Tuna-Luna/Team5_Alligaeator/src/project/nutrition_db.py

# nutrition_db.py 
FOOD_DB = {
    0: {"food": "bean sprouts",     "kcal": 155, "protein": 13.0, "carbs": 1.1, "fat": 11.0},
    1: {"food": "beef", "kcal": 239, "protein": 27.0, "carbs": 0.0, "fat": 14.0},
    2: {"food": "chicken",  "kcal": 149, "protein": 6.4,  "carbs": 33.0, "fat": 0.5},
    3: {"food": "egg",     "kcal": 155, "protein": 13.0, "carbs": 1.1, "fat": 11.0},
    4: {"food": "fork", "kcal": 239, "protein": 27.0, "carbs": 0.0, "fat": 14.0},
    5: {"food": "garlic",  "kcal": 149, "protein": 6.4,  "carbs": 33.0, "fat": 0.5},
    6: {"food": "green onion",     "kcal": 155, "protein": 13.0, "carbs": 1.1, "fat": 11.0},
    7: {"food": "kimchi", "kcal": 239, "protein": 27.0, "carbs": 0.0, "fat": 14.0},
    8: {"food": "onion",  "kcal": 149, "protein": 6.4,  "carbs": 33.0, "fat": 0.5},
    9: {"food": "potato",     "kcal": 155, "protein": 13.0, "carbs": 1.1, "fat": 11.0},
    10: {"food": "spam", "kcal": 239, "protein": 27.0, "carbs": 0.0, "fat": 14.0},
     
}
